jie326513988/mini-T12/Picture/1.jpg

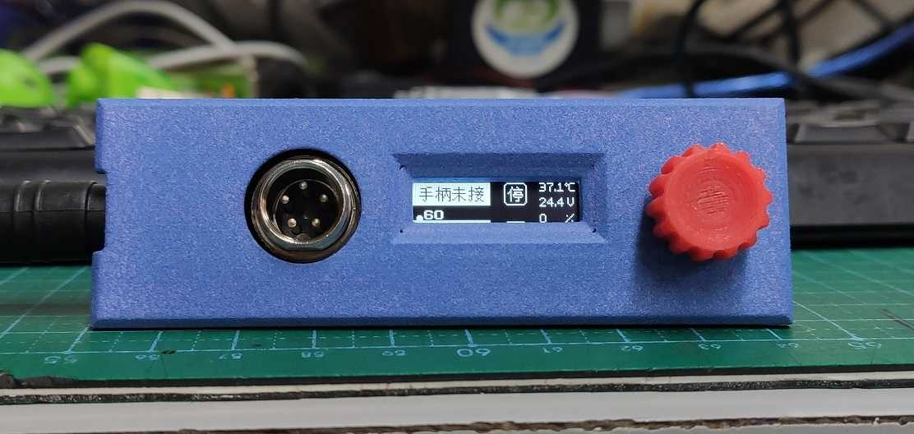
Picture/1.jpg
